mpangch/OpenRiggingPlate/FEA Analysis/Test 1 (2697.7 lbf)/Deformation.png

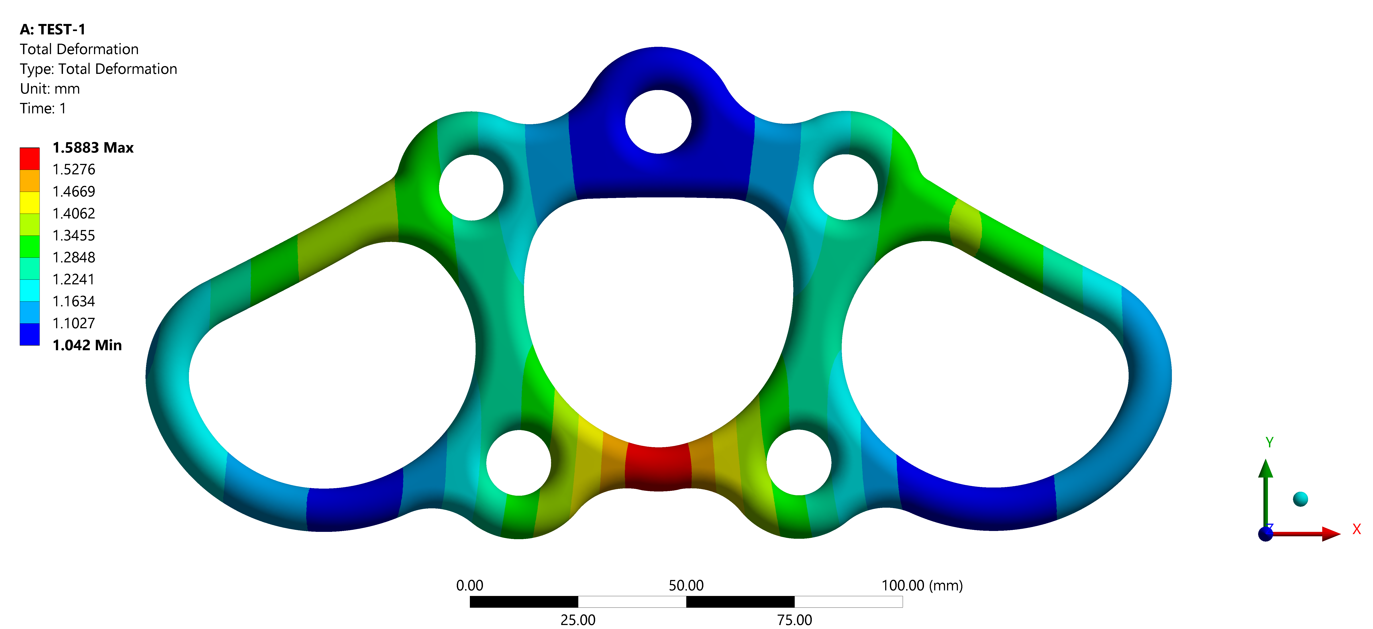
FEA Analysis/Test 1 (2697.7 lbf)/Deformation.png
