mpangch/OpenRiggingPlate/FEA Analysis/Test 1 (2697.7 lbf)/Safety Factor.png

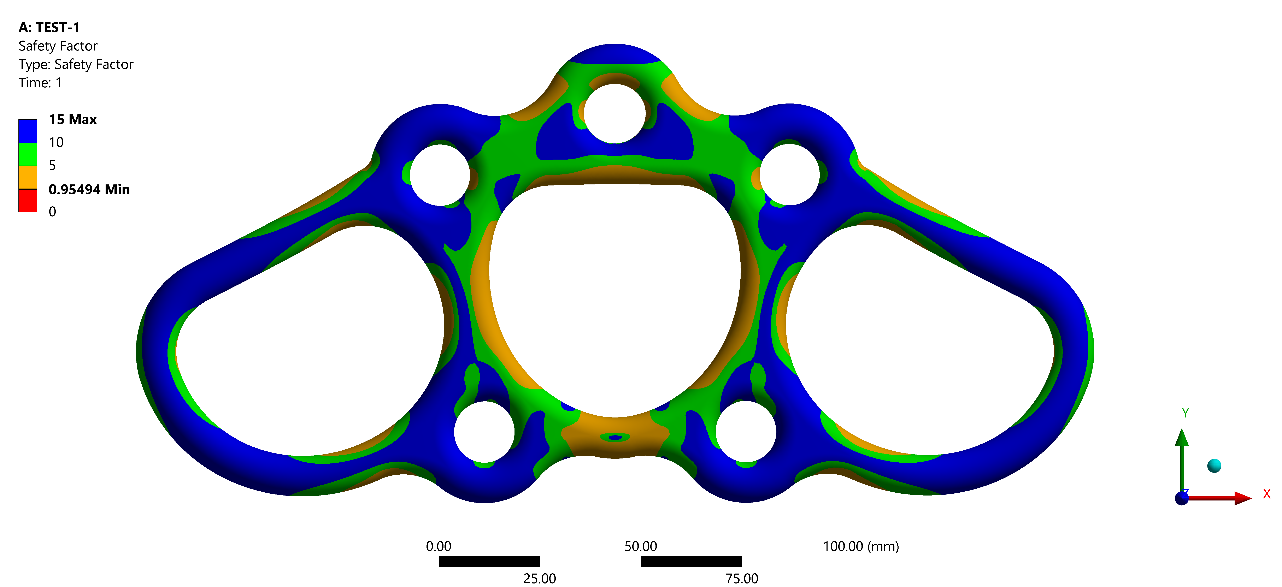
FEA Analysis/Test 1 (2697.7 lbf)/Safety Factor.png
