mpangch/OpenRiggingPlate/FEA Analysis/Test 3 (4768.8 lbf)/Safety Factor.png

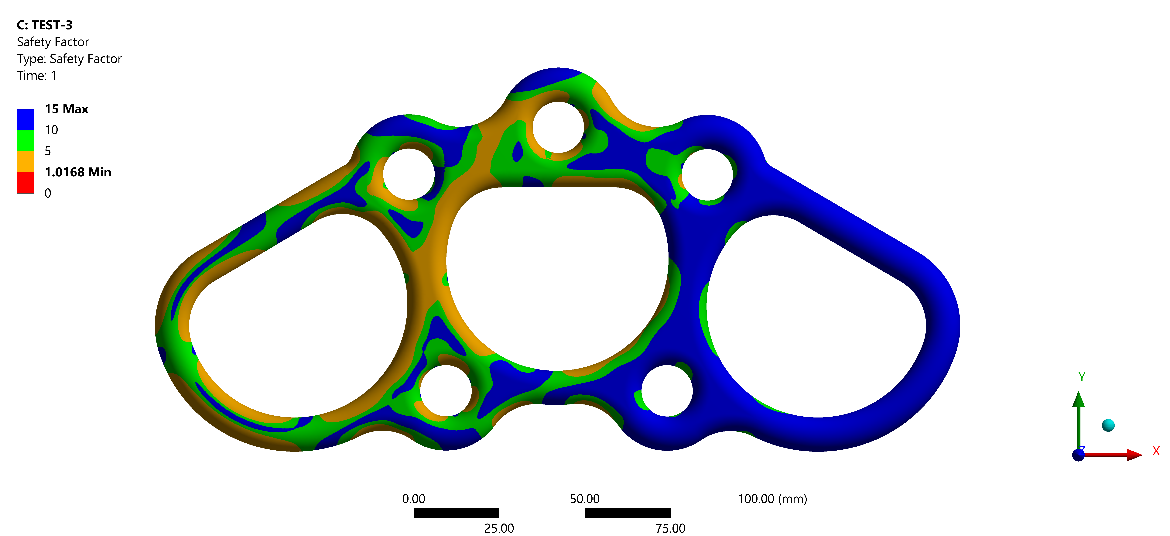
FEA Analysis/Test 3 (4768.8 lbf)/Safety Factor.png
