mpangch/OpenRiggingPlate/FEA Analysis/Test 4 (2225.4 lbf)/Boundary Conditions.png

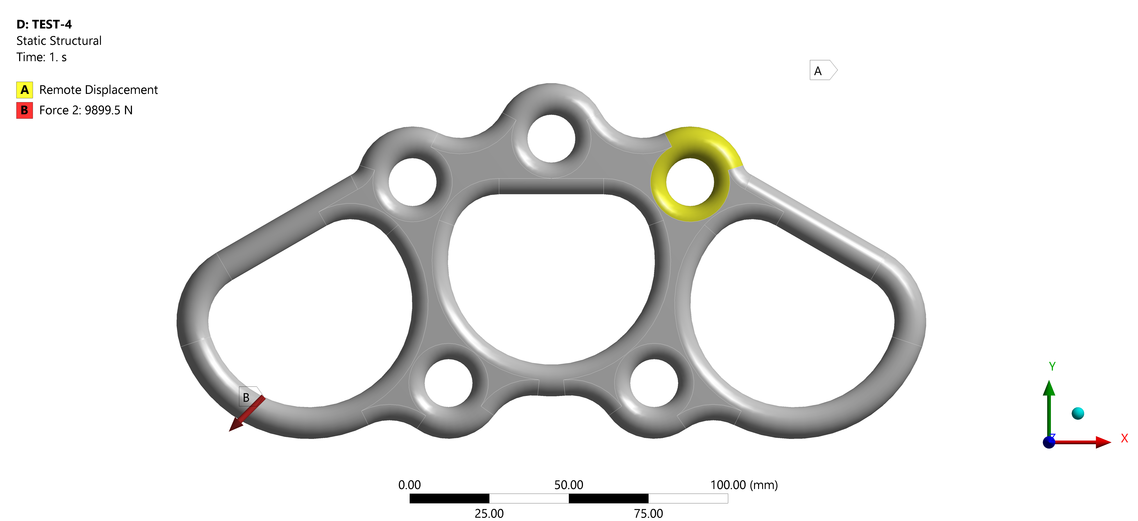
FEA Analysis/Test 4 (2225.4 lbf)/Boundary Conditions.png
