mpangch/OpenRiggingPlate/FEA Analysis/Test 4 (2225.4 lbf)/Deformation.png

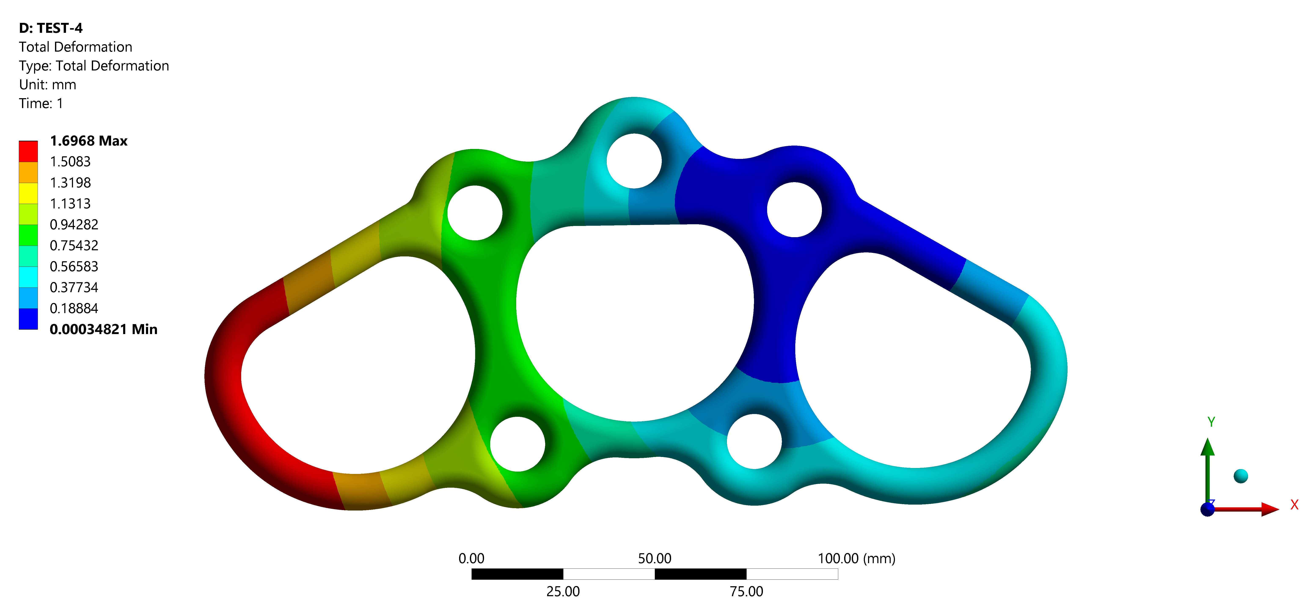
FEA Analysis/Test 4 (2225.4 lbf)/Deformation.png
