mpangch/OpenRiggingPlate/FEA Analysis/Test 4 (2225.4 lbf)/Stress.png

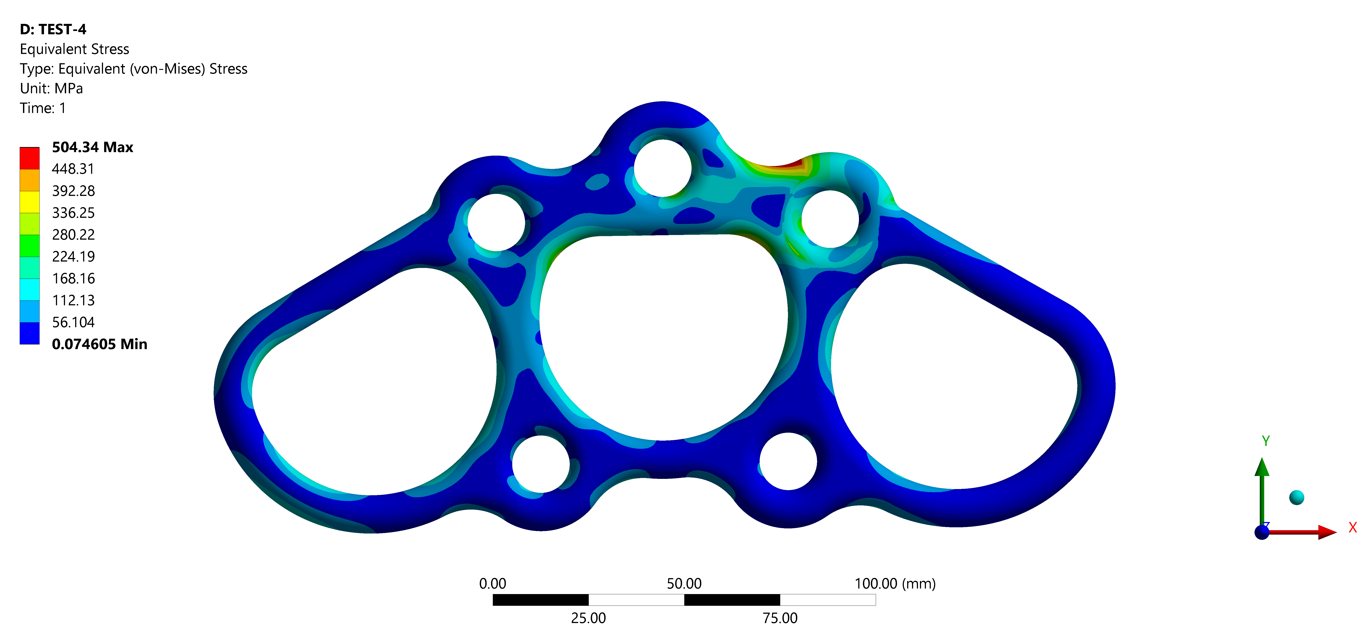
FEA Analysis/Test 4 (2225.4 lbf)/Stress.png
