mpangch/OpenRiggingPlate/FEA Analysis/Test 5 (2810.1 lbf)/Boundary Conditions.png

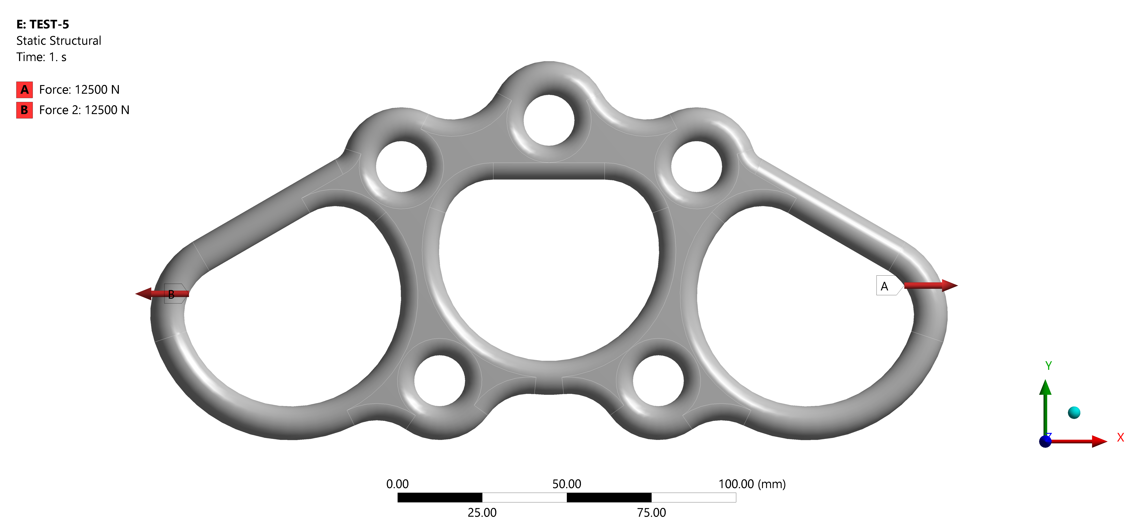
FEA Analysis/Test 5 (2810.1 lbf)/Boundary Conditions.png
