mpangch/OpenRiggingPlate/FEA Analysis/Test 5 (2810.1 lbf)/Deformation.png

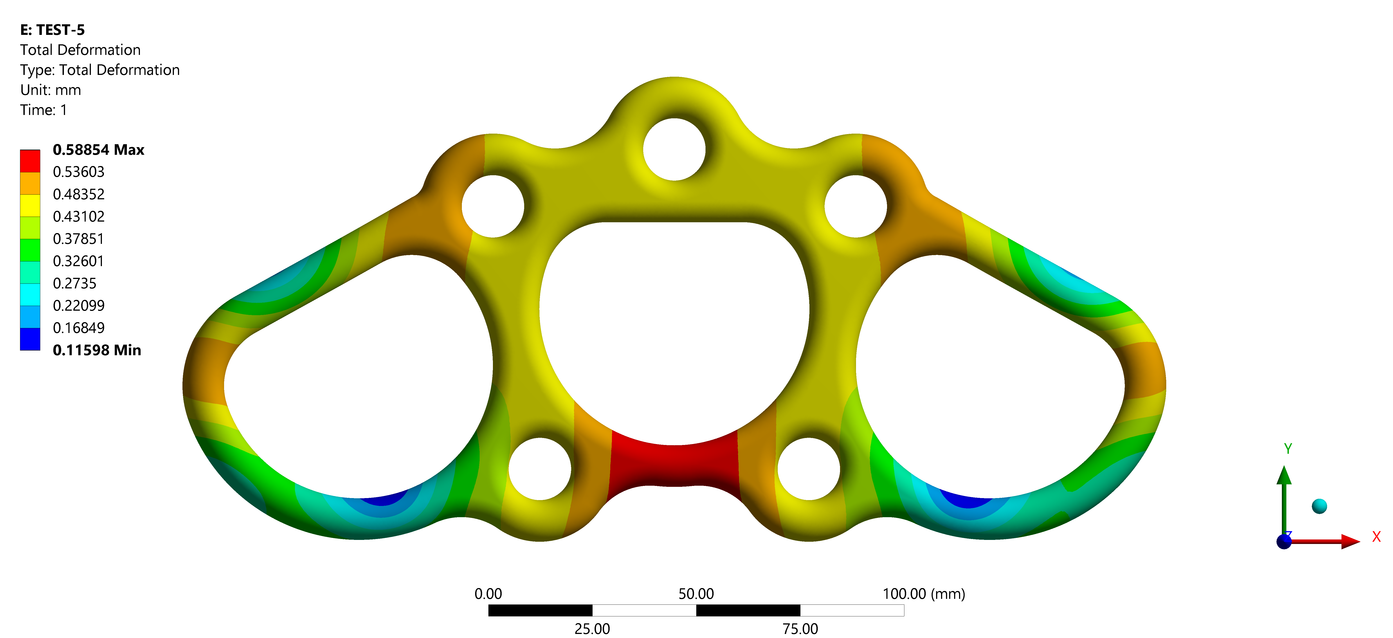
FEA Analysis/Test 5 (2810.1 lbf)/Deformation.png
