mpangch/OpenRiggingPlate/FEA Analysis/Test 5 (2810.1 lbf)/Stress.png

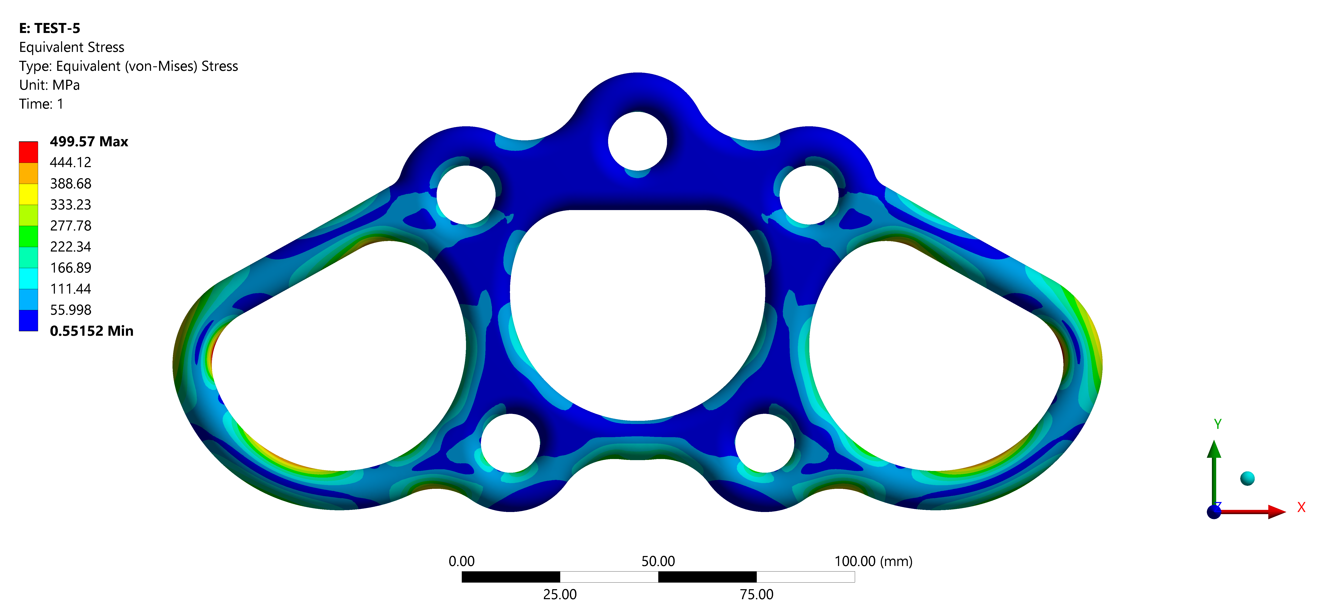
FEA Analysis/Test 5 (2810.1 lbf)/Stress.png
