mpangch/OpenRiggingPlate/FEA Analysis/Test 6 (3372.1 lbf)/Boundary Conditions.png

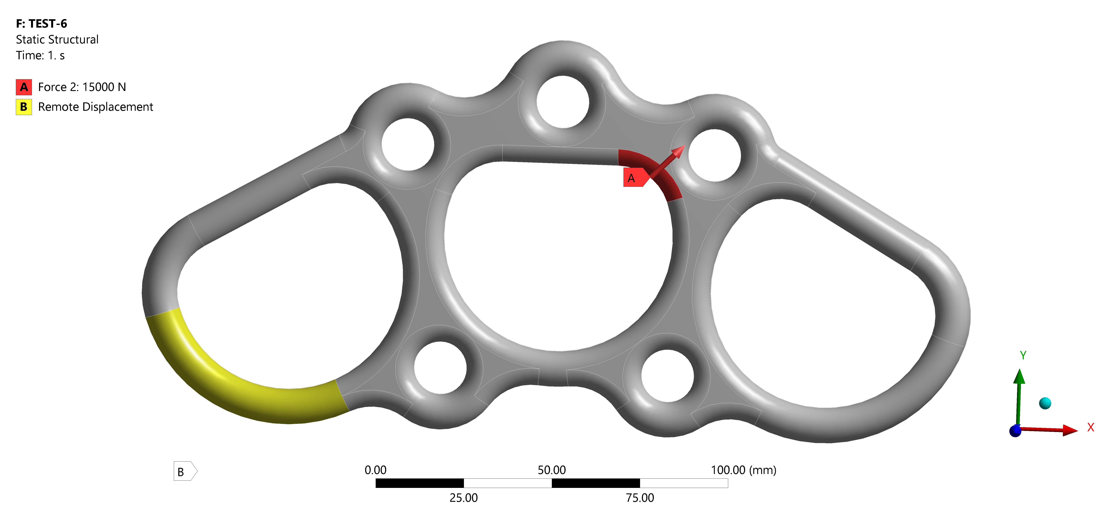
FEA Analysis/Test 6 (3372.1 lbf)/Boundary Conditions.png
