mpangch/OpenRiggingPlate/FEA Analysis/Test 6 (3372.1 lbf)/Deformation.png

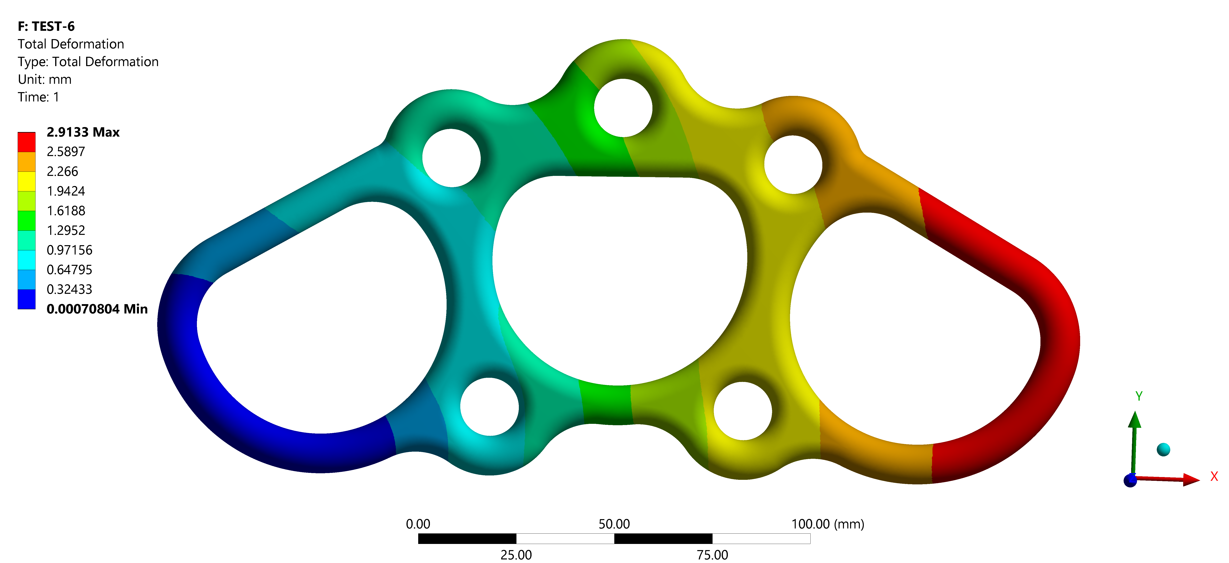
FEA Analysis/Test 6 (3372.1 lbf)/Deformation.png
