mpangch/OpenRiggingPlate/FEA Analysis/Test 6 (3372.1 lbf)/Safety Factor.png

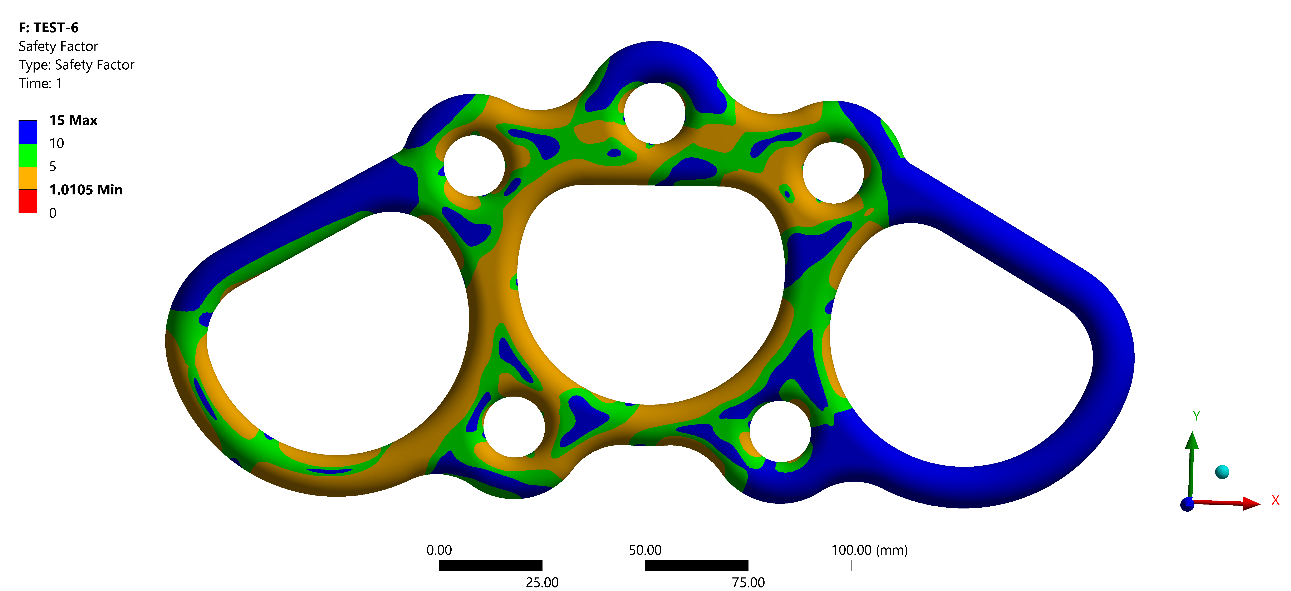
FEA Analysis/Test 6 (3372.1 lbf)/Safety Factor.png
